Brillar0101/pen-mixer/production/output/board-bottom.png

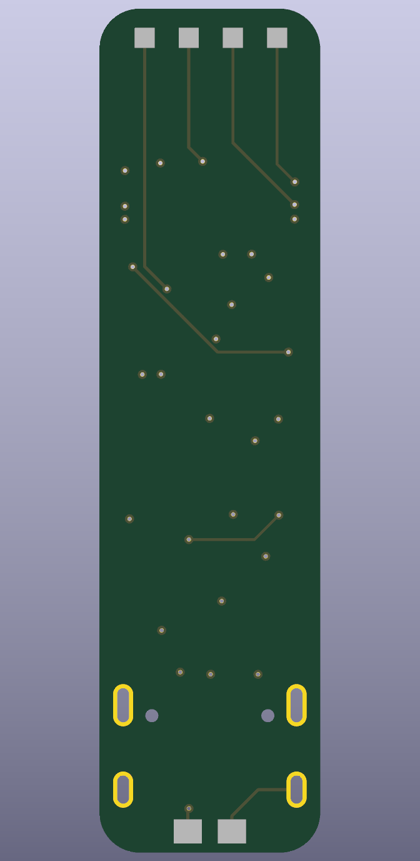
production/output/board-bottom.png
