Brillar0101/pen-mixer/production/output/board-top.png

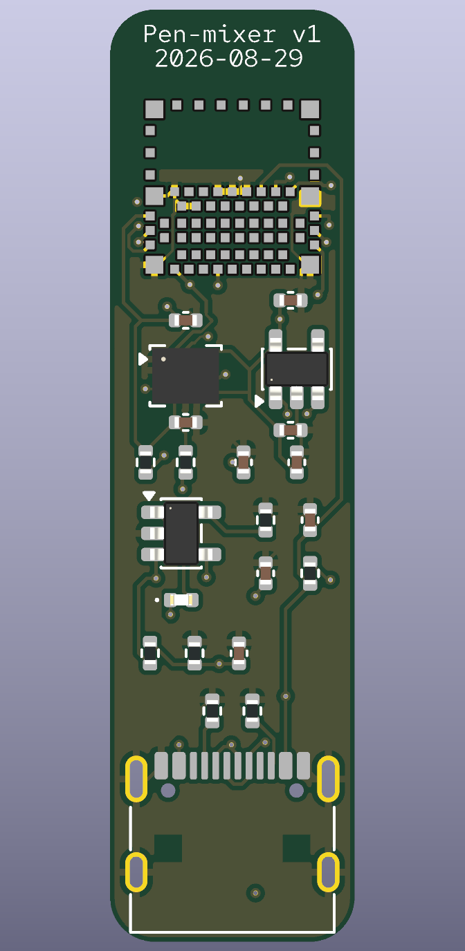
production/output/board-top.png
