Brillar0101/pen-mixer/production/output/v3/v3-star-top.png

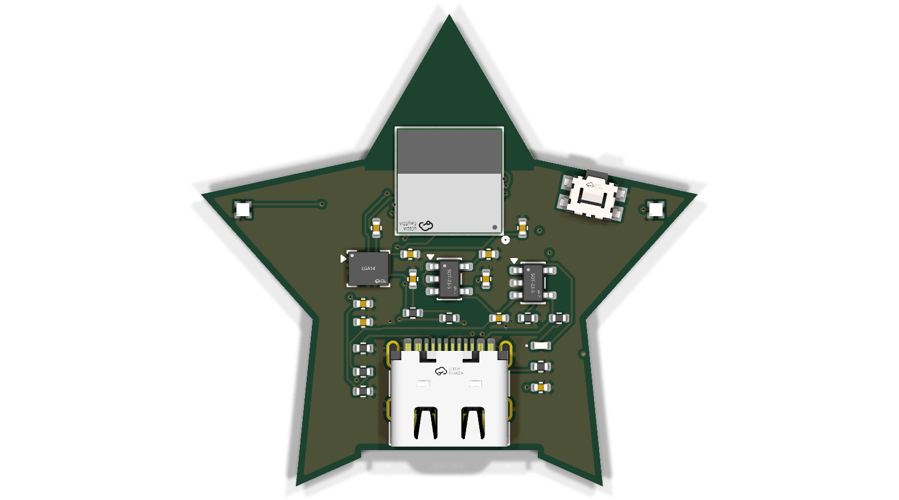
production/output/v3/v3-star-top.png
